YuraSergienko/GAME500/src/User/game500.h

#define DATA0 GPIO_Pin_3    // PA3
#define DATA1 GPIO_Pin_5    // PA5
#define DATA2 GPIO_Pin_4    // PA4
#define DATA3 GPIO_Pin_6    // PA6
#define DATA4 GPIO_Pin_7    // PA7
#define DATA5 GPIO_Pin_8    // PA8
#define DATA6 GPIO_Pin_11   // PA11
#define DATA7 GPIO_Pin_12   // PA12
#define ADDR0 GPIO_Pin_9    // PB9
#define ADDR1 GPIO_Pin_8    // PB8
#define ADDR2 GPIO_Pin_7    // PB7
#define ADDR3 GPIO_Pin_6    // PB6
#define ADDR4 GPIO_Pin_5    // PB5
#define ADDR5 GPIO_Pin_4    // PB4
#define ADDR6 GPIO_Pin_10   // PB10
#define ADDR7 GPIO_Pin_11   // PB11
#define ADDR12 GPIO_Pin_0   // BP0
#define LED_R GPIO_Pin_13
#define LED_G GPIO_Pin_1
#define LED_B GPIO_Pin_2
#define SPI_CLK GPIO_Pin_13
#define SPI_DI GPIO_Pin_15
#define SPI_DO GPIO_Pin_14
#define SPI_CS GPIO_Pin_12
#define AUDIO GPIO_Pin_1
#define PLAY GPIO_Pin_0

#define NW 170 // Tape speed. More - lower speed, less - higher speed

// function declarations ------------------------------------------------------------------
void gpio_init(void);
void flash_init1(void);
void my_rcc_init(void);
void play_loader(void);
uint8_t read_flash(uint16_t f_addr, uint16_t b_addr);
void write_PU2(uint8_t PU_data);

// variable declarations ------------------------------------------------------------------
uint8_t     ADDR12_line=0;
uint8_t     PU_addr = 0;
uint16_t    PU_addr_in = 0;
uint8_t     PU_data = 0;
uint16_t    PU_data_out = 0;
uint8_t     file_addrH = 0;
uint8_t     file_addrL = 0;
uint16_t    file_addr = 0;
uint16_t    file_len = 0;
uint8_t     file_byte = 0;
uint16_t    byte_addr = 0;
uint8_t     MODE1_FLAG = 0;
uint8_t     MODE2_FLAG = 0;
//uint8_t     temp_byte = 0;

// loader1 CASSETE ---------------------------------------------------------------------------
static const uint8_t loader1[2000] = {
        0x00,0x00,0x00,0x00,0x00,0x00,0x00,0x00,0x00,0x00,0x00,0x00,0x00,0x00,0x00,0x00,0x00,0x00,0x00,0x00,0x00,0x00,0x00,0x00,0x00, // pilottone
        0x55,0x55,0x55,0x55,0x55,0x55,0x55,0x55,0x55,0x55,0x55,0x55,0x55,0x55,0x55,0x55,0x55,0x55,0x55,0x55,0x55,0x55,0x55,0x55,0x55, // pilottone
        0x00,0x00,0x00,0x00,0x00,0x00,0x00,0x00,0x00,0x00,0x00,0x00,0x00,0x00,0x00,0x00,0x00,0x00,0x00,0x00,0x00,0x00,0x00,0x00,0x00, // pilottone
        0x55,0x55,0x55,0x55,0x55,0x55,0x55,0x55,0x55,0x55,0x55,0x55,0x55,0x55,0x55,0x55,0x55,0x55,0x55,0x55,0x55,0x55,0x55,0x55,0x55, // pilottone
        0x00,0x00,0x00,0x00,0x00,0x00,0x00,0x00,0x00,0x00,0x00,0x00,0x00,0x00,0x00,0x00,0x00,0x00,0x00,0x00,0x00,0x00,0x00,0x00,0x00, // pilottone
        0x55,0x55,0x55,0x55,0x55,0x55,0x55,0x55,0x55,0x55,0x55,0x55,0x55,0x55,0x55,0x55,0x55,0x55,0x55,0x55,0x55,0x55,0x55,0x55,0x55, // pilottone
        0x00,0x00,0x00,0x00,0x00,0x00,0x00,0x00,0x00,0x00,0x00,0x00,0x00,0x00,0x00,0x00,0x00,0x00,0x00,0x00,0x00,0x00,0x00,0x00,0x00, // pilottone
        0x55,0x55,0x55,0x55,0x55,0x55,0x55,0x55,0x55,0x55,0x55,0x55,0x55,0x55,0x55,0x55,0x55,0x55,0x55,0x55,0x55,0x55,0x55,0x55,0x55, // pilottone
//200
        0x00,0x00,0x00,0x00,0x00,0x00,0x00,0x00,0x00,0x00,0x00,0x00,0x00,0x00,0x00,0x00,  // block marker
//216
        0x55,0x55,0x55,0x55,0xe6, // subblock0 marker
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
        0x10, 0xD3, 0x05, 0x13, 0x13, 0x13, 0x13, 0x13, 0x13, 0x13, 0x13, 0x13, 0x13, 0x13, 0x3E, 0x00,
        0xD3, 0x05, 0xC3, 0x00, 0x01, 0x00, 0x00, 0x00, 0x00, 0x00, 0x00, 0x00, 0x00, 0x00, 0x00, 0x00,
        0x00, 0x00, 0x00, 0x00, 0x00, 0x00, 0x00, 0x00, 0x00, 0x00, 0x00, 0x00, 0x00, 0x00, 0x00, 0x00,
        0x00, 0x00, 0x00, 0x00, 0x00, 0x00, 0x00, 0x00, 0x00, 0x00, 0x00, 0x00, 0x00, 0x00, 0x00, 0x00,
        0x00, 0x00, 0x00, 0x00, 0x00, 0x00, 0x00, 0x00, 0x00, 0x00, 0x00, 0x00, 0x00, 0x00, 0x55, 0xAA
};
